cracked-machine/FunctionGeneratorCortexM4_HW/HW/ControlsBoard/RevE/ControlsBoard/ControlsBoard.kicad_pcb

## KiCad design HW/ControlsBoard/RevE/ControlsBoard/ControlsBoard.kicad_pcb (2020-05-30)

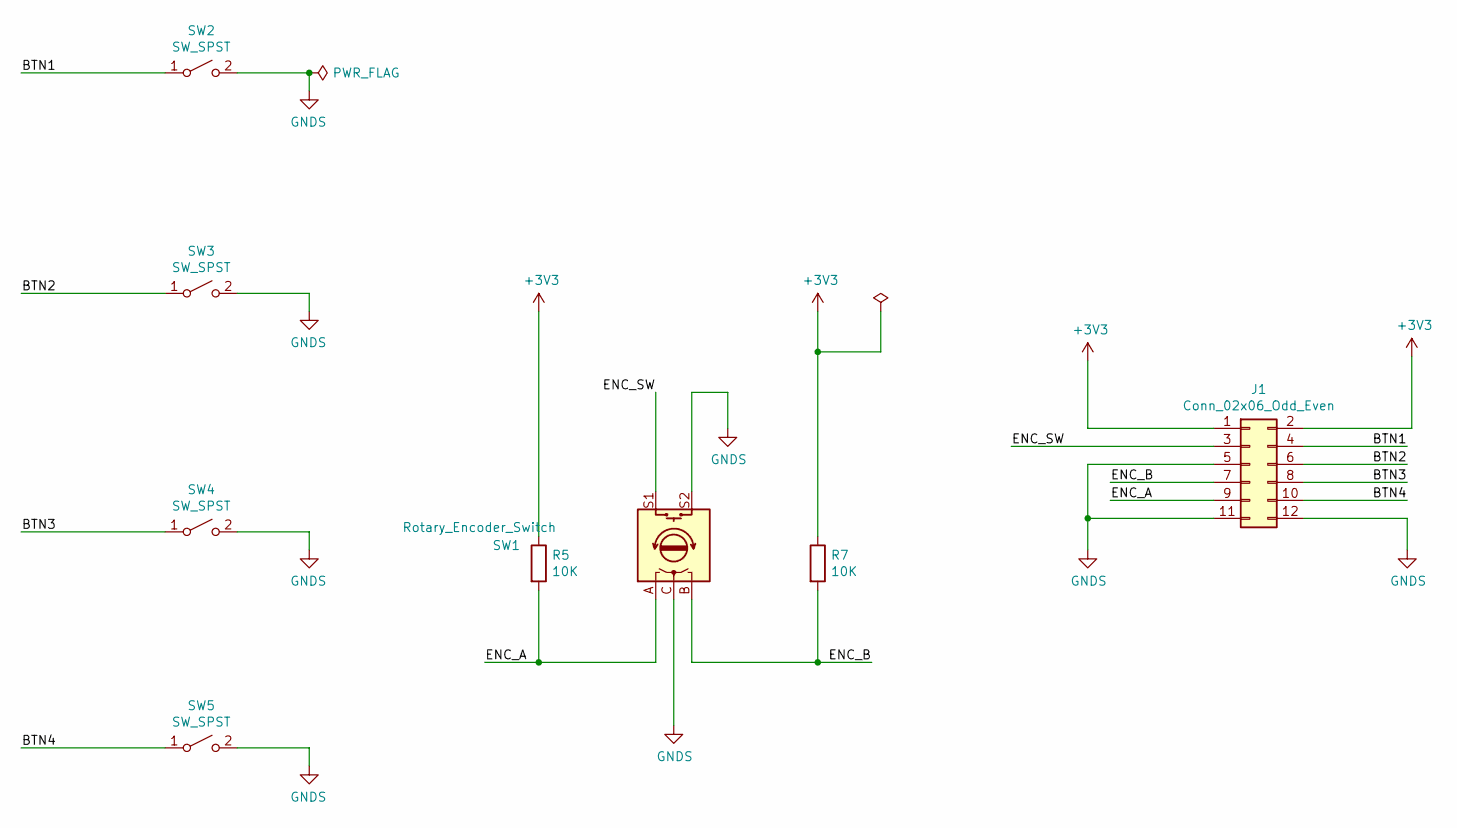
[picture p20: schematic Controls.sch]

Parts:
J1: Conn_02x06_Odd_Even; PinSocket_2x06_P2.54mm_Vertical_SMD
R5, R7: 10K; R_1206_3216Metric_Pad1.42x1.75mm_HandSolder
SW1: Rotary_Encoder_Switch; RotaryEncoder_Alps_EC11E-Switch_Vertical_H20mm
SW2, SW3, SW4, SW5: SW_SPST; SW_PUSH_6mm

Connections:
+3V3: J1.1, J1.2, R5.1, R7.1
/Controls/BTN1: J1.4, SW2.1 (A)
/Controls/BTN2: J1.6, SW3.1 (A)
/Controls/BTN3: J1.8, SW4.1 (A)
/Controls/BTN4: J1.10, SW5.1 (A)
/Controls/ENC_A: J1.9, R5.2, SW1.A
/Controls/ENC_B: J1.7, R7.2, SW1.B
/Controls/ENC_SW: J1.3, SW1.S1
GNDS: J1.5, J1.11, J1.12, SW1.C, SW1.S2, SW2.2 (B), SW3.2 (B), SW4.2 (B), SW5.2 (B)

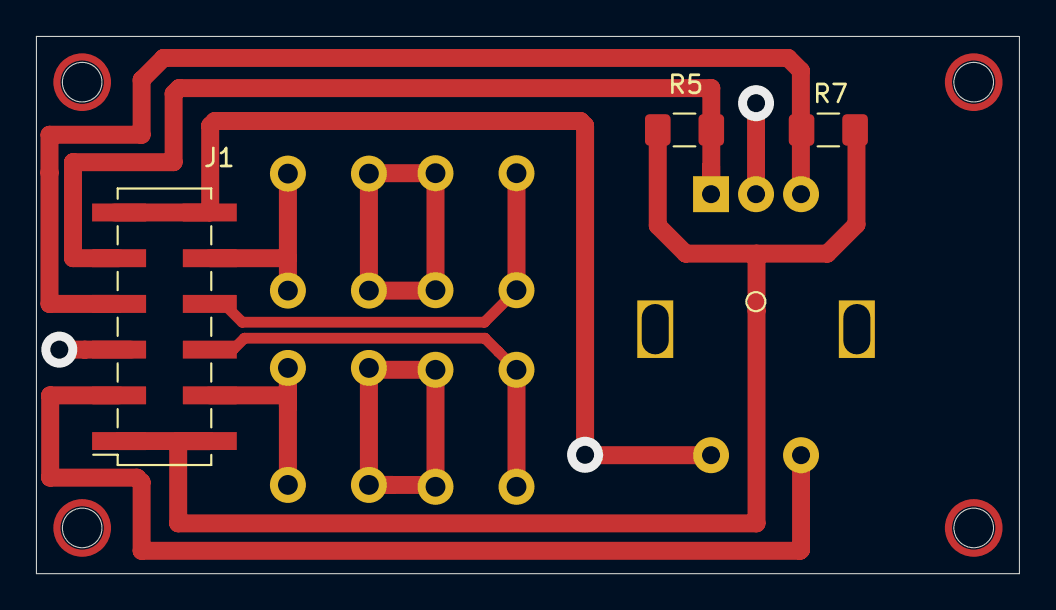
[picture p21: board HW/ControlsBoard/RevE/ControlsBoard/ControlsBoard.kicad_pcb from above]

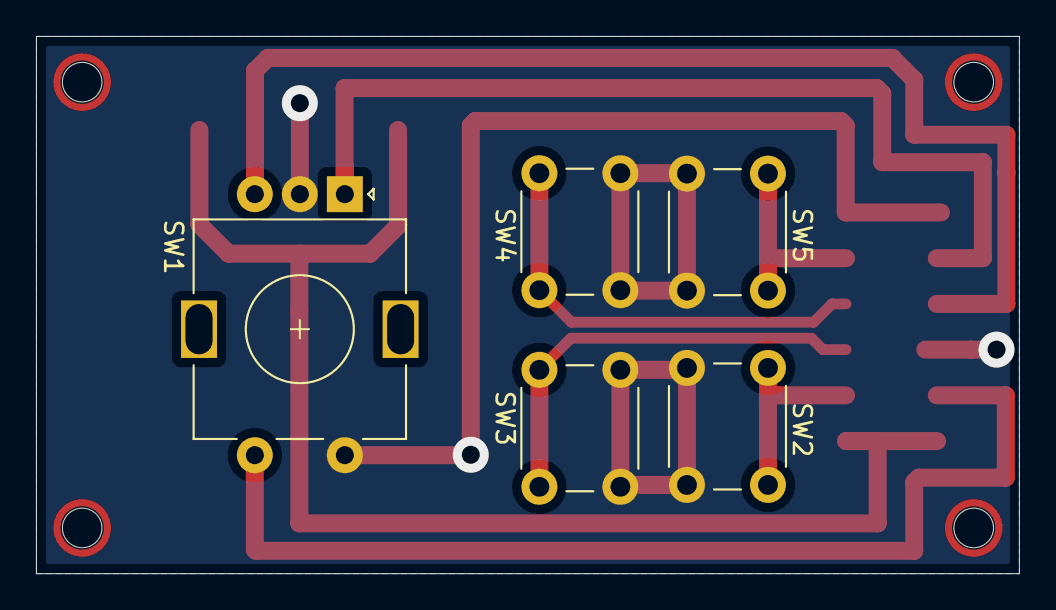
[picture p22: board HW/ControlsBoard/RevE/ControlsBoard/ControlsBoard.kicad_pcb from below]

Board: 2 copper layers, 54.6 x 29.8 mm, 8 parts (5 on the bottom side), 9 nets.
