cracked-machine/FunctionGeneratorCortexM4_HW/HW/MainBoard/RevC/FunctionGeneratorCortexM4/FunctionGeneratorCortexM4.kicad_pcb

## KiCad design HW/MainBoard/RevC/FunctionGeneratorCortexM4/FunctionGeneratorCortexM4.kicad_pcb (2020-03-15)

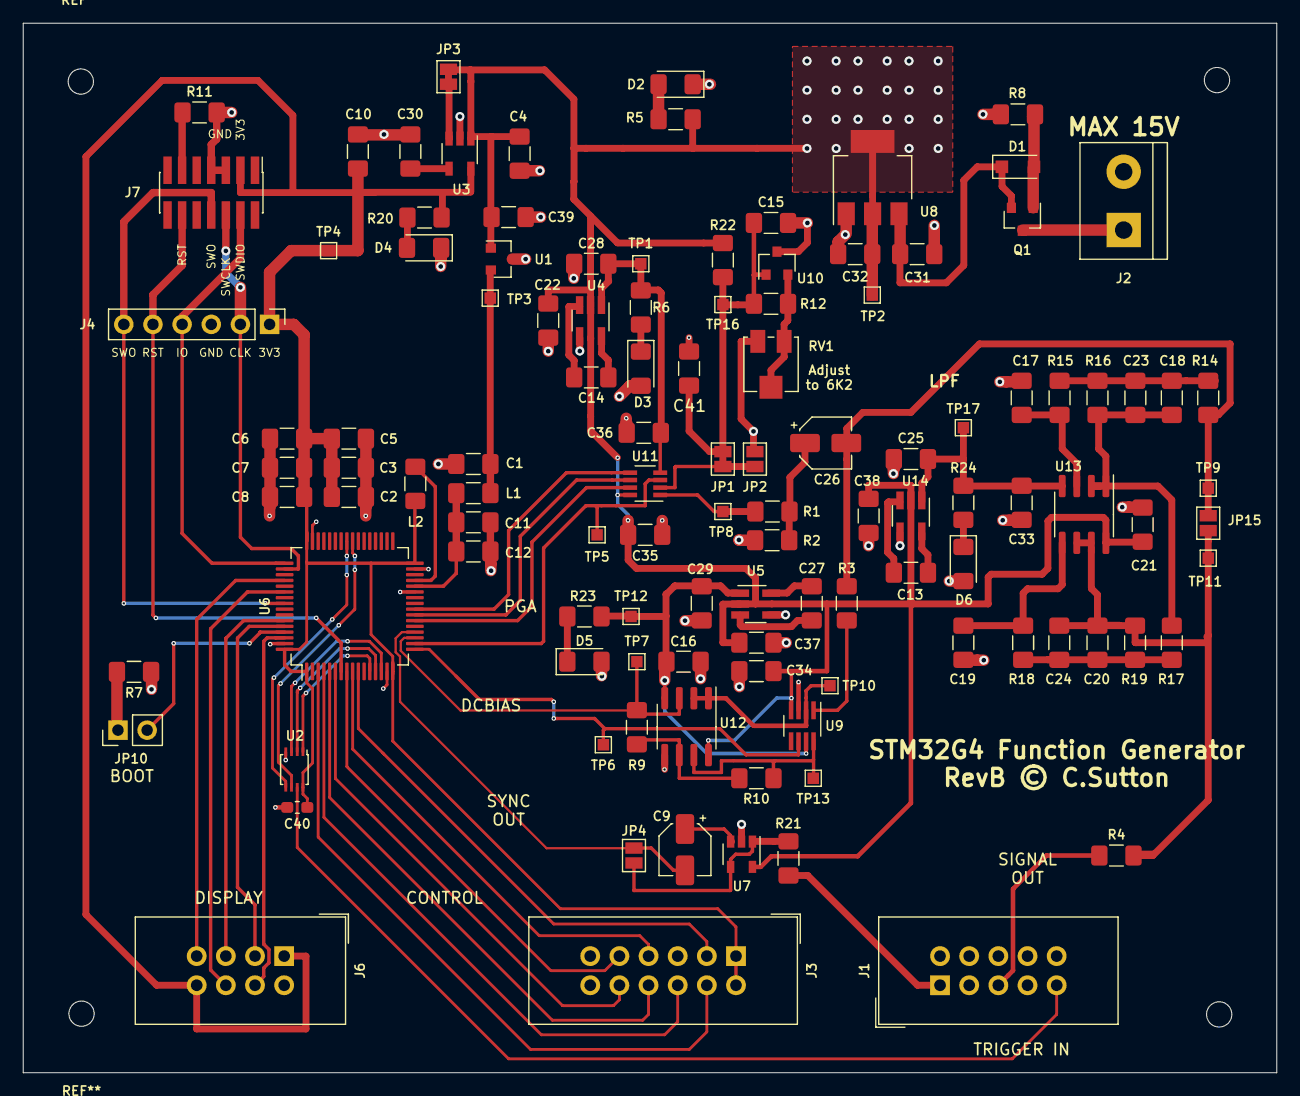
[picture p23: board FunctionGeneratorCortexM4.kicad_pcb from above]

Board: 2 copper layers, 109.2 x 91.4 mm, 115 parts (0 on the bottom side), 77 nets.

Parts:
C1, C5, C6, C7, C8, C12, C16, C21, C22, C31, C33, C34, C35, C36, C37, C38, C39: 100nF; C_1206_3216Metric_Pad1.42x1.75mm_HandSolder
C2, C4, C10, C11, C30, C41: 1uF; C_1206_3216Metric_Pad1.42x1.75mm_HandSolder
C3: 4.7uF; C_1206_3216Metric_Pad1.42x1.75mm_HandSolder
C9, C26: 10uF; CP_Elec_4x5.7
C13, C14, C25, C27, C28, C29: 10Uf; C_1206_3216Metric_Pad1.42x1.75mm_HandSolder
C15, C17, C18, C19, C20, C23, C24: 1nF; C_1206_3216Metric_Pad1.42x1.75mm_HandSolder
C32: 10uF; C_1206_3216Metric_Pad1.42x1.75mm_HandSolder
C40: 100nF; C_0603_1608Metric_Pad1.05x0.95mm_HandSolder
D1: 10V; D_SOD-123F
D2, D3, D4, D5, D6: LED; LED_1206_3216Metric_Pad1.42x1.75mm_HandSolder
J1: Conn_02x05_Odd_Even; IDC-Header_2x05_P2.54mm_Vertical
J2: Screw_Terminal_01x02; TerminalBlock_bornier-2_P5.08mm
J3: Conn_02x06_Odd_Even; IDC-Header_2x06_P2.54mm_Vertical
J4: Conn_01x06; PinHeader_1x06_P2.54mm_Vertical
J6: Conn_02x04_Odd_Even; IDC-Header_2x04_P2.54mm_Vertical
J7: Conn_02x07_Odd_Even; PinHeader_2x07_P1.27mm_Vertical_SMD
JP1, JP3: Jumper_NC_Small; SolderJumper-2_P1.3mm_Bridged_Pad1.0x1.5mm
JP2, JP4, JP15: Jumper_NO_Small; SolderJumper-2_P1.3mm_Open_Pad1.0x1.5mm
JP10: Jumper_NC_Small; PinHeader_1x02_P2.54mm_Vertical
L1, L2: 600R@100MHz; L_1206_3216Metric_Pad1.42x1.75mm_HandSolder
Q1: DMG2301L; SOT-23
R1: 560R; R_1206_3216Metric_Pad1.42x1.75mm_HandSolder
R2, R3, R7, R12: 10K; R_1206_3216Metric_Pad1.42x1.75mm_HandSolder
R4, R21: 50R; R_1206_3216Metric_Pad1.42x1.75mm_HandSolder
R5, R6, R20, R23, R24: 4K7; R_1206_3216Metric_Pad1.42x1.75mm_HandSolder
R8: 100K; R_1206_3216Metric_Pad1.42x1.75mm_HandSolder
R9, R10, R14, R15, R16, R17, R18, R19, R22: 1K; R_1206_3216Metric_Pad1.42x1.75mm_HandSolder
R11: 100R; R_1206_3216Metric_Pad1.42x1.75mm_HandSolder
RV1: R_POT_TRIM; Potentiometer_Bourns_3314J_Vertical
TP1, TP2, TP3, TP4, TP5, TP6, TP7, TP8, TP9, TP10, TP11, TP12, TP13, TP16, TP17: TestPoint; TestPoint_Pad_1.0x1.0mm
U1: NCP51460SN33T1G; SOT-23
U2: TS5A3357; VSSOP-8_2.4x2.1mm_P0.5mm
U3: LP3992-33B5F; TSOT-23-5
U4, U5, U14: TPS60400; SOT-23-5_HandSoldering
U6: STM32G474RET; LQFP-64_10x10mm_P0.5mm
U7: MCP601-xOT; SOT-23-5
U8: LM1117-5.0; SOT-223-3_TabPin2
U9: TS12A12511DCNR; SOT-23-8_Handsoldering
U10: TL431DBZ; SOT-23
U11: LTC6910; TSOT-23-8
U12, U13: TL072; SOIC-8_3.9x4.9mm_P1.27mm

Connections:
/+2.5V: C15.1, C41.2, JP1.1, R12.1, R22.1, TP16.1, U10.1
/+3V3: C2.1, C3.1, C5.1, C6.1, C7.1, C8.1, C10.1, C40.1, J3.1, J3.2, J4.1, J6.1, J6.8, J7.3, L2.1, R20.1, TP4.1, U2.8, U3.5, U6.1, U6.16, U6.32, U6.48, U6.64
/+5V: C4.1, C21.1, C22.1, C32.1, C34.2, C35.2, C37.1, C38.1, C39.1, JP3.1, R5.1, R22.2, TP2.1, U1.1, U3.1, U4.2, U5.2, U7.5, U8.2, U9.4, U11.8, U12.8, U13.8, U14.2
/-5V_DCBIAS: C16.2, C29.2, R23.1, TP12.1, U5.1, U9.7, U12.4
/-5V_LPF: C25.2, C33.1, R24.1, TP17.1, U13.4, U14.1
/-5V_PGA: C28.2, C36.2, R6.1, TP1.1, U4.1, U11.4
/AnalogOutput/DCBIAS: R3.2, U9.1
/AnalogOutput/DCBIAS_INVERT_IN: TP6.1, U6.17, U9.6
/AnalogOutput/SG0_IN: U6.24, U11.5
/AnalogOutput/SG1_IN: U6.23, U11.6
/AnalogOutput/SG2_IN: U6.22, U11.7
/FUNC_SIG_OUT: J1.5, R4.1
/FUNC_SYNC_OUT: J1.1, R21.1
/MCU/ADC_IN3: U2.3, U6.14
/MCU/BTN1: J3.4, U6.3
/MCU/BTN2: J3.6, U6.4
/MCU/BTN3: J3.8, U6.5
/MCU/BTN4: J3.10, U6.6
/MCU/COMP1_INP: U2.2, U6.13
/MCU/ENC_A: J3.9, U6.8
/MCU/ENC_B: J3.7, U6.9
/MCU/ENC_SW: J3.3, U6.10
/MCU/FUNC1_DCBIAS: R9.2, TP7.1, U6.19, U12.3
/MCU/FUNC1_SIG: TP5.1, U6.18, U11.3
/MCU/FUNC1_SYNC: C9.2, JP4.1, U6.20
/MCU/TFT_CS: J6.3, U6.60
/MCU/TFT_DC: J6.5, U6.59
/MCU/TFT_MOSI: J6.6, U6.54
/MCU/TFT_RST: J6.4, U6.62
/MCU/TFT_SCK: J6.7, U6.52
/MCU/TIM2_TF1FP1: U2.1, U6.12
/MCU/TRIGMUX1: U2.6, U6.40
/MCU/TRIGMUX2: U2.5, U6.41
/MCU/T_NRST: J4.5, J7.12, U6.7
/MCU/T_SWCLK: J4.2, J7.6, U6.50
/MCU/T_SWDIO: J4.4, J7.4, U6.49
/MCU/T_SWO: J4.6, J7.8, U6.56
/PSU/3V3REF: C1.1, L1.1, TP3.1, U1.2
/PSU/VIN: J2.1, Q1.3
/TRIG_SIG_IN: J1.9, U2.7
GNDS: C1.2, C2.2, C3.2, C4.2, C5.2, C6.2, C7.2, C8.2, C10.2, C11.1, C12.1, C15.2, C16.1, C17.1, C19.1, C21.2, C22.2, C25.1, C28.1, C29.1, C30.2, C31.2, C32.2, C33.2, C34.1, C35.1, C36.1, C37.2, C38.2, C39.2, C40.2, C41.1, D2.1, D3.2, D4.1, D5.2, D6.2, J1.2, J1.3, J1.4, J1.6, J1.7, J1.8, J1.10, J2.2, J3.5, J3.11, J3.12, J4.3, J6.2, J7.5, J7.7, JP2.2, R2.1, R7.1, R8.2, R11.2, RV1.3, U1.3, U2.4, U3.2, U4.4, U5.4, U6.15, U6.27, U6.31, U6.47, U6.63, U7.2, U8.1, U9.3, U10.3, U12.5, U14.4
unnamed: C9.1, U7.3
unnamed: C11.2, C12.2, L1.2, U6.28
unnamed: C13.1, U14.3
unnamed: C13.2, U14.5
unnamed: C14.1, U4.3
unnamed: C14.2, U4.5
unnamed: C17.2, R15.1, U13.3
unnamed: C18.1, C23.1, R16.1, R17.2, U13.1, U13.2
unnamed: C18.2, C23.2, R14.1, R15.2, R16.2
unnamed: C19.2, R18.1, U13.5
unnamed: C20.1, C24.1, JP15.2, R4.2, R19.1, TP11.1, U13.6, U13.7
unnamed: C20.2, C24.2, R17.1, R18.2, R19.2
unnamed: C26.1, R1.2, R2.2
unnamed: C26.2, JP15.1, R3.1, R14.2, TP9.1
unnamed: C27.1, U5.3
unnamed: C27.2, U5.5
unnamed: C30.1, U3.4
unnamed: C31.1, D1.1, Q1.2, U8.3
unnamed: D1.2, Q1.1, R8.1
unnamed: D2.2, R5.2
unnamed: D3.1, R6.2
unnamed: D4.2, R20.2
unnamed: D5.1, R23.2
unnamed: D6.1, R24.2
unnamed: J7.11, R11.1
unnamed: JP1.2, JP2.1, U11.2
unnamed: JP3.2, U3.3
unnamed: JP4.2, R21.2, U7.1, U7.4
unnamed: JP10.1, R7.2
unnamed: JP10.2, U6.61
unnamed: L2.2, U6.29
unnamed: R1.1, TP8.1, U11.1
unnamed: R10.1, TP13.1, U9.8, U12.7
unnamed: R9.1, R10.2, U12.6
unnamed: R12.2, RV1.1, RV1.2, U10.2
unnamed: TP10.1, U9.2, U12.1, U12.2
