cracked-machine/FunctionGeneratorCortexM4_HW/HW/IOBoard/RevB/IOBoard/IOBoard.kicad_pcb

## KiCad design HW/IOBoard/RevB/IOBoard/IOBoard.kicad_pcb (2020-04-12)

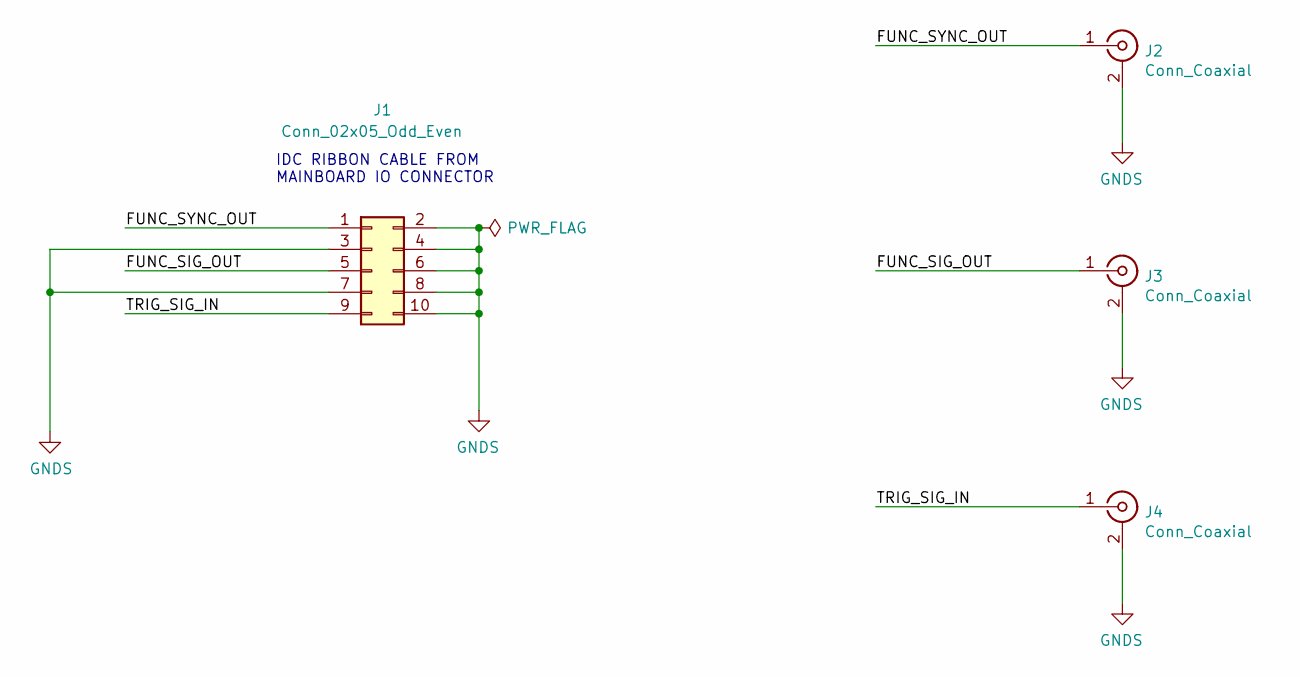
[picture p24: schematic IOBoard.sch]

Parts:
J1: Conn_02x05_Odd_Even; PinHeader_2x05_P2.54mm_Vertical_SMD
J2, J3, J4: Conn_Coaxial; RSProStraight50OhmPCBMountBulkheadFittingBNC_5260279

Connections:
/FUNC_SIG_OUT: J1.5, J3.1 (In)
/FUNC_SYNC_OUT: J1.1, J2.1 (In)
/TRIG_SIG_IN: J1.9, J4.1 (In)
GNDS: J1.2, J1.3, J1.4, J1.6, J1.7, J1.8, J1.10, J2.2 (Ext), J3.2 (Ext), J4.2 (Ext)

Notes on the sheet:
IDC RIBBON CABLE FROM MAINBOARD IO CONNECTOR

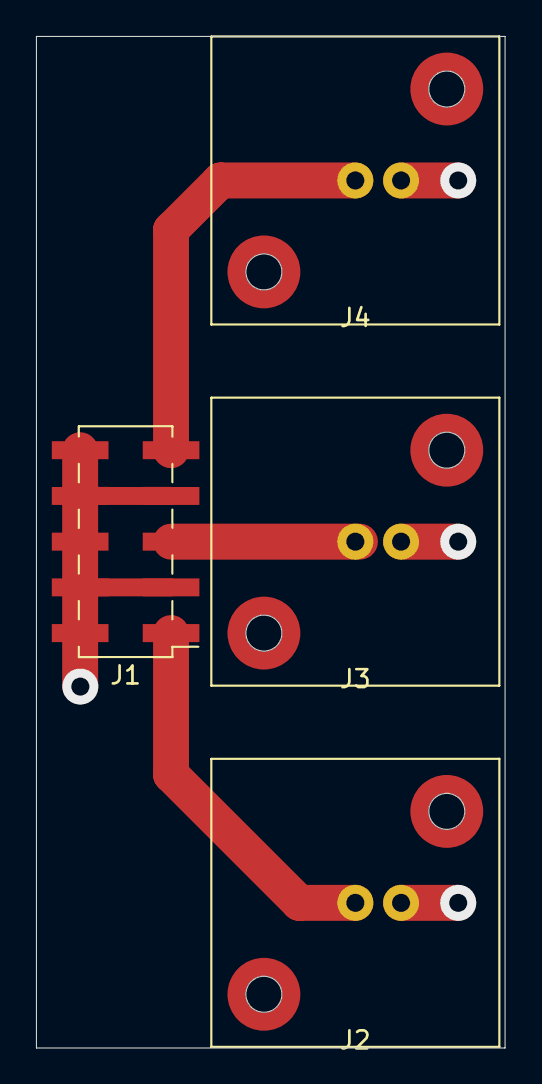
[picture p25: board IOBoard.kicad_pcb from above]

Board: 2 copper layers, 26.0 x 56.2 mm, 4 parts (0 on the bottom side), 4 nets.
