cracked-machine/FunctionGeneratorCortexM4_HW/HW/ControlsBoard/RevD/ControlsBoard/ControlsBoard.kicad_pcb

## KiCad design HW/ControlsBoard/RevD/ControlsBoard/ControlsBoard.kicad_pcb (2020-05-30, an earlier design)

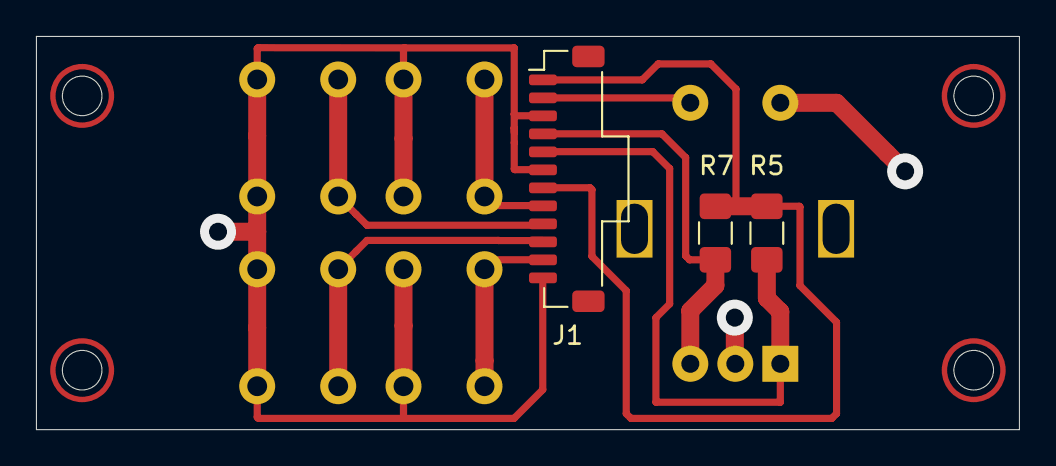
[picture p26: board HW/ControlsBoard/RevD/ControlsBoard/ControlsBoard.kicad_pcb from above]

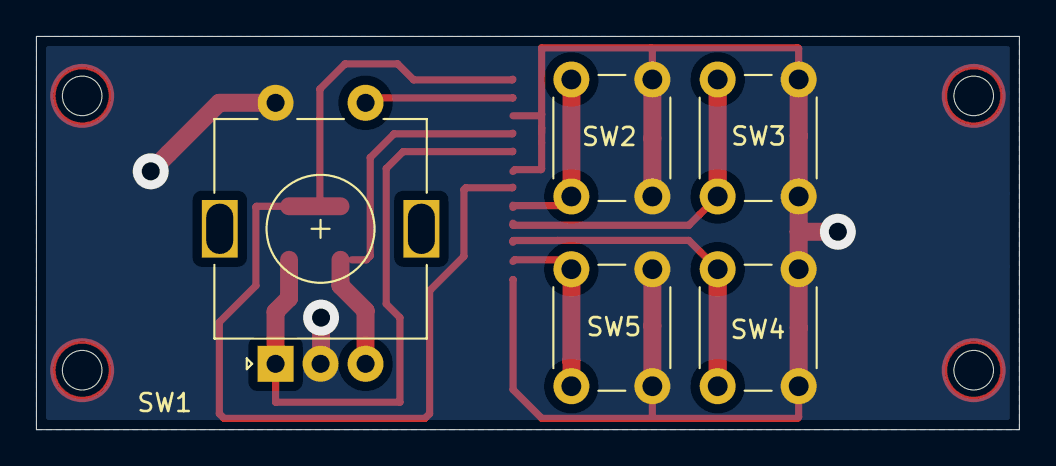
[picture p27: board HW/ControlsBoard/RevD/ControlsBoard/ControlsBoard.kicad_pcb from below]

Board: 2 copper layers, 54.6 x 21.8 mm, 8 parts (5 on the bottom side), 9 nets.

Parts:
J1: Conn_01x12; Molex_Pico-Clasp_501331-1207_1x12-1MP_P1.00mm_Vertical
R5, R7: 10K; R_1206_3216Metric_Pad1.42x1.75mm_HandSolder
SW1: Rotary_Encoder_Switch; RotaryEncoder_Alps_EC11E-Switch_Vertical_H20mm
SW2, SW3, SW4, SW5: SW_SPST; SW_PUSH_6mm

Connections:
+3V3: J1.1, J1.7, R5.1, R7.1
/Controls/BTN1: J1.8, SW2.1
/Controls/BTN2: J1.9, SW3.1
/Controls/BTN3: J1.10, SW4.1
/Controls/BTN4: J1.11, SW5.1
/Controls/ENC_A: J1.5, R5.2, SW1.A
/Controls/ENC_B: J1.4, R7.2, SW1.B
/Controls/ENC_SW: J1.2, SW1.S1
GNDS: J1.3, J1.6, J1.12, SW1.C, SW1.S2, SW2.2, SW3.2, SW4.2, SW5.2
