cracked-machine/FunctionGeneratorCortexM4_HW/HW/ControlsBoard/RevA/ControlsBoard/ControlsBoard.kicad_pcb

## KiCad design HW/ControlsBoard/RevA/ControlsBoard/ControlsBoard.kicad_pcb (2020-04-06, an earlier design)

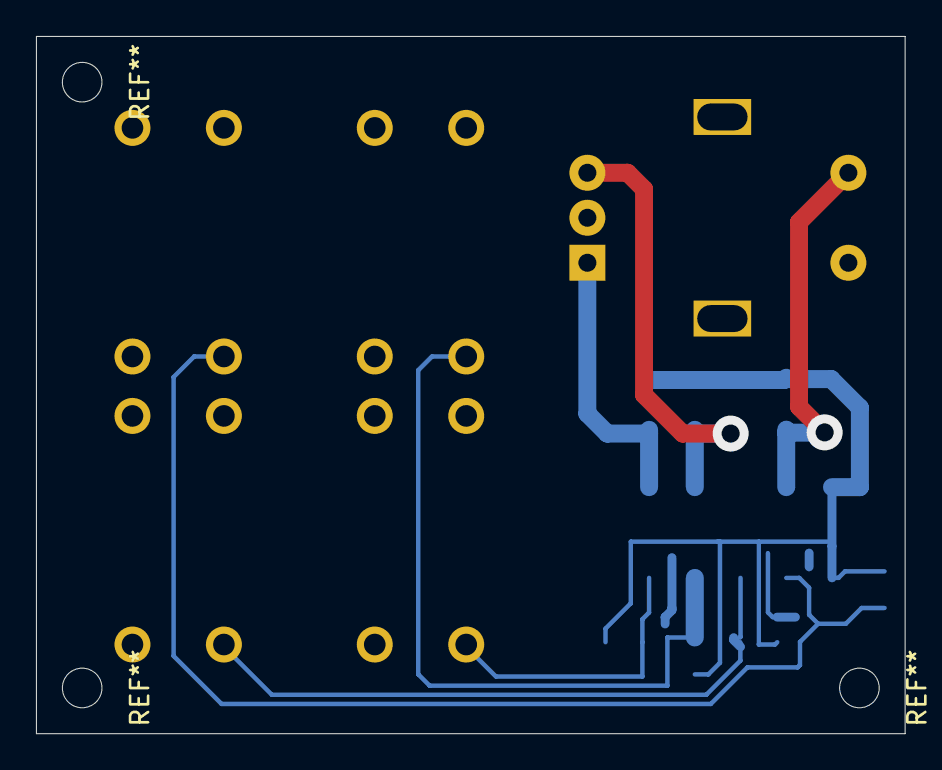
[picture p28: board HW/ControlsBoard/RevA/ControlsBoard/ControlsBoard.kicad_pcb from above]

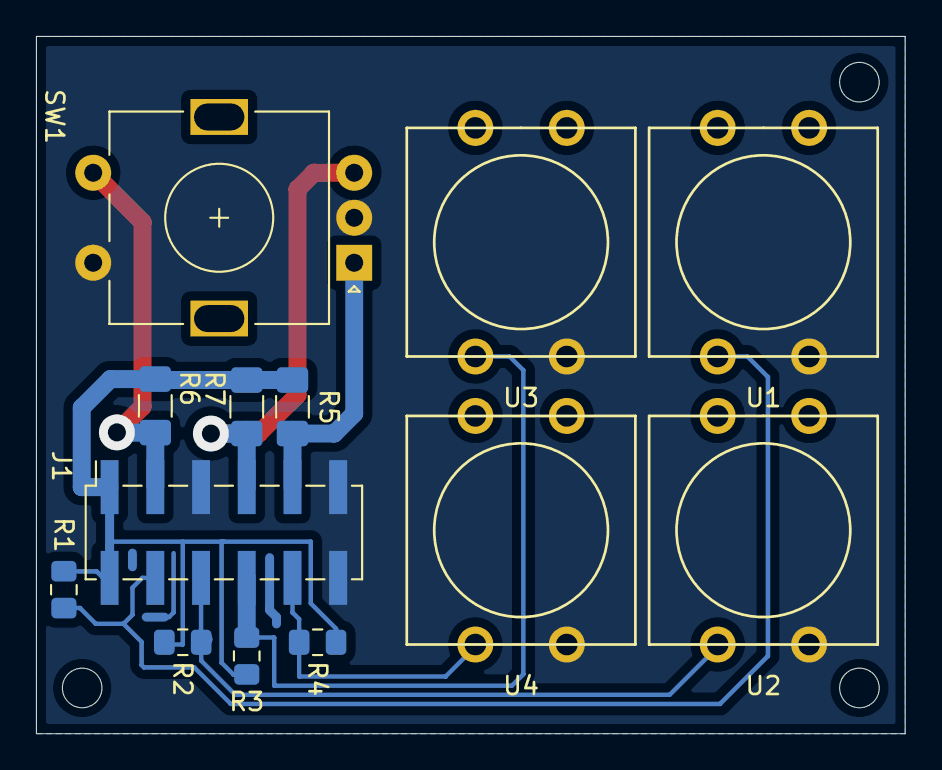
[picture p29: board HW/ControlsBoard/RevA/ControlsBoard/ControlsBoard.kicad_pcb from below]

Board: 2 copper layers, 48.3 x 38.7 mm, 13 parts (13 on the bottom side), 9 nets.

Parts:
J1: Conn_02x06_Odd_Even; PinSocket_2x06_P2.54mm_Vertical_SMD
R1, R2, R3, R4: 220R; R_0805_2012Metric_Pad1.15x1.40mm_HandSolder
R5, R6, R7: 10K; R_1206_3216Metric_Pad1.42x1.75mm_HandSolder
SW1: Rotary_Encoder_Switch; RotaryEncoder_Alps_EC11E-Switch_Vertical_H20mm
U1, U2, U3, U4: Tactile_Switch_SPST-NO; 12x12x7_3mmTactilePushButtonMomentary

Connections:
+3V3: J1.1, J1.2, R1.1, R2.1, R3.1, R4.1, R5.1, R6.1, R7.1
/Controls/BTN1: J1.4, R1.2, U1.4
/Controls/BTN2: J1.6, R2.2, U2.4
/Controls/BTN3: J1.8, R3.2, U3.4
/Controls/BTN4: J1.10, R4.2, U4.4
/Controls/ENC_A: J1.9, R5.2, SW1.A
/Controls/ENC_B: J1.7, R7.2, SW1.B
/Controls/ENC_SW: J1.3, R6.2, SW1.S1
GNDS: J1.5, J1.11, J1.12, SW1.C, SW1.S2, U1.2, U2.2, U3.2, U4.2
